drkmsmithjr/NixiePowerSupply/SimCalcFiles/EfficiencyVsInputVoltage.jpg

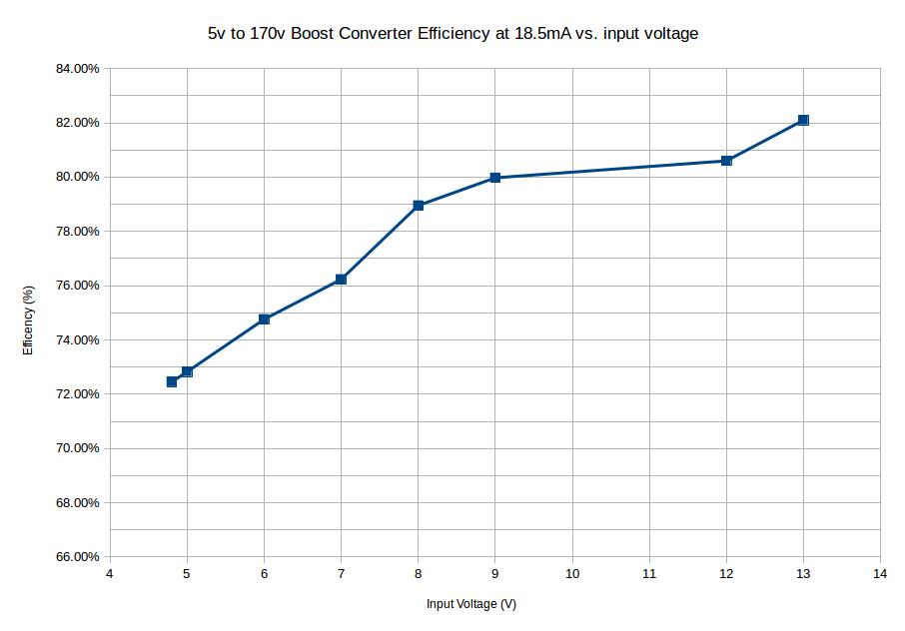
SimCalcFiles/EfficiencyVsInputVoltage.jpg
