drkmsmithjr/NixiePowerSupply/SimCalcFiles/BoostSupply_160v.asc

C1: cap; 2µF
C2: cap; 220pF
C3: cap; 150e-6; Lser=.05n
C4: cap; 330pF
C5: cap; 200p
C7: cap; 10pF
C8: cap; 100pF
C9: cap; 47µ
C10: cap; 10p; Rser=10m
D1: schottky; UPSC600
D2: diode; 1N4148
D3: schottky; UPSC600
L1: ind; 33µH; Rser=.045
L2: ind; 100n; Rser=.02
R1: res; .1
R2: res; 1k
R3: res; 634k
R4: res; 7.5k
R5: res; 60k
R6: res; .1
R7: res; 2k
R8: res; 100k
R9: res; 9k
R10: res; 100k
R12: res; 20
R13: res; 100k
S1: sw; MySwitch2
S2: sw; FETU
U1: UCC3803
V1: voltage; 5; Rser=.01
V4: voltage; PULSE(0 5 25m 5n 5n 15m 60m); Rser=10
Named nets: 0, Vout, SW
.tran 0 80m 0 50n
.ic V(Vout) = 160
.model MySwitch2 SW(Ron=.01 Roff=10Meg Vt=2.5 Vh=.05)
.options gmin=1e-10
.options abstol=1e-10
.options reltol=.003
.options cshunt=1e-15
.model FETU SW(Ron= 70m Roff=10MEG Vt=0.8 Vh=-0.3)
18mA pulsed Load
Minimal Load
