drkmsmithjr/NixiePowerSupply/SimCalcFiles/StepResponse.jpg

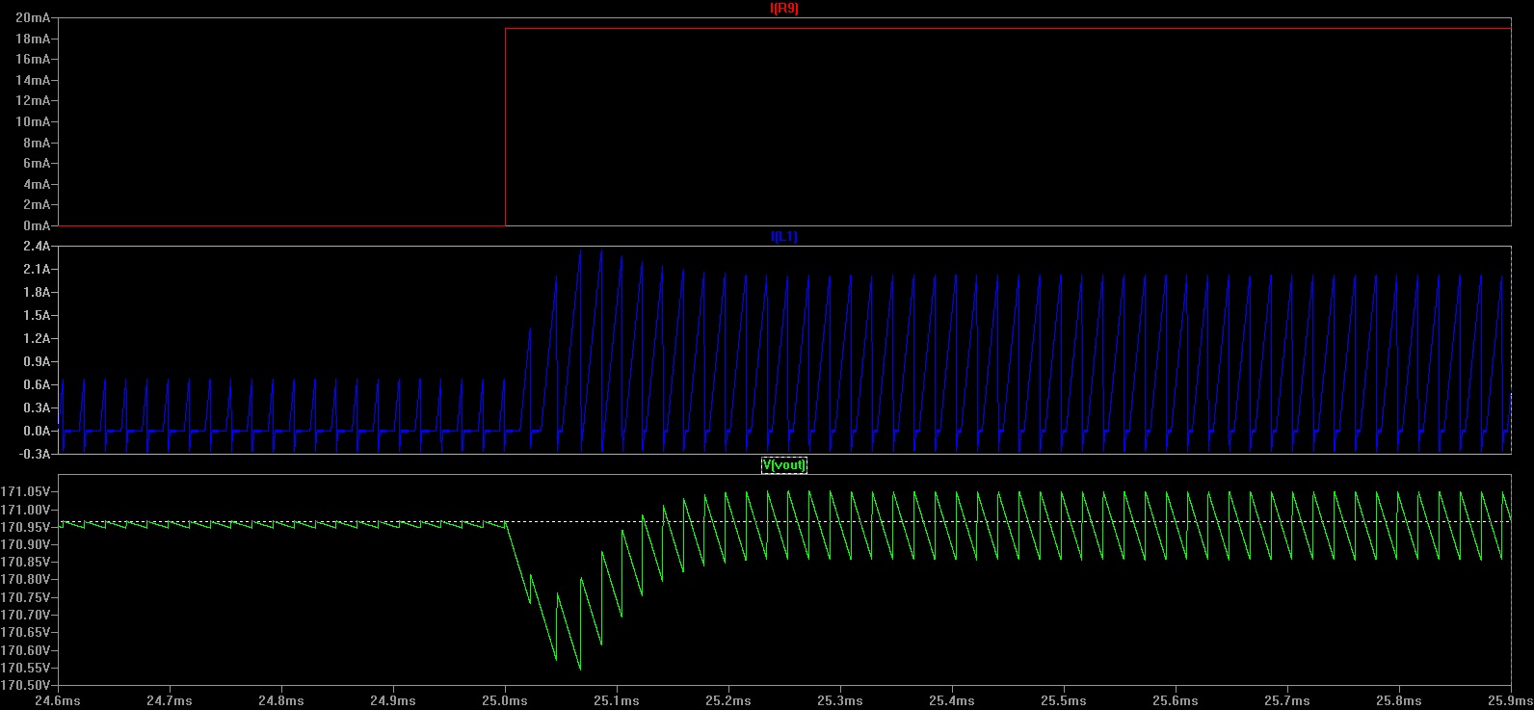
SimCalcFiles/StepResponse.jpg
